V3lectronics/SPIRIT/branding/headphonejack.png

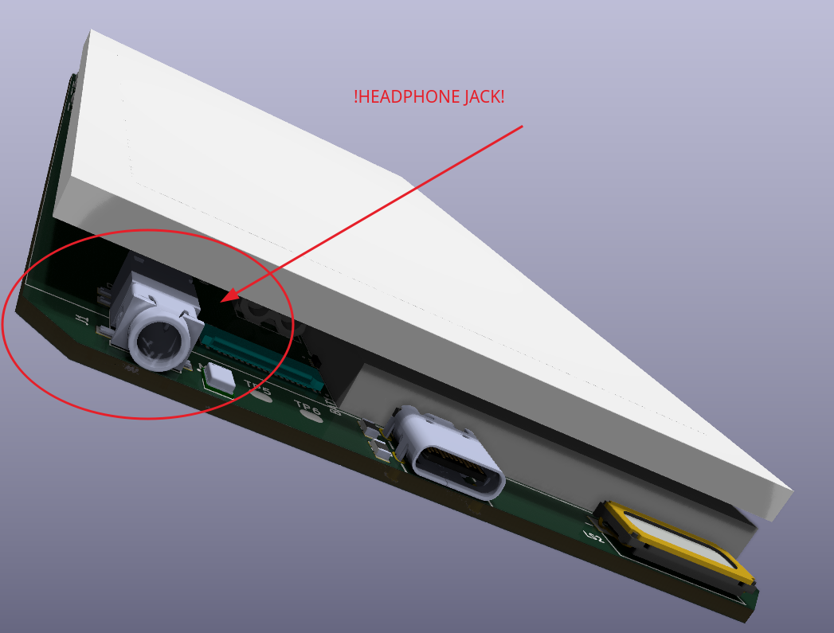
branding/headphonejack.png
