V3lectronics/SPIRIT/EDA-kicad/component-libs/SPIRIT-3D-models/CC0805MKX5R5BB476-capacitor.STEP

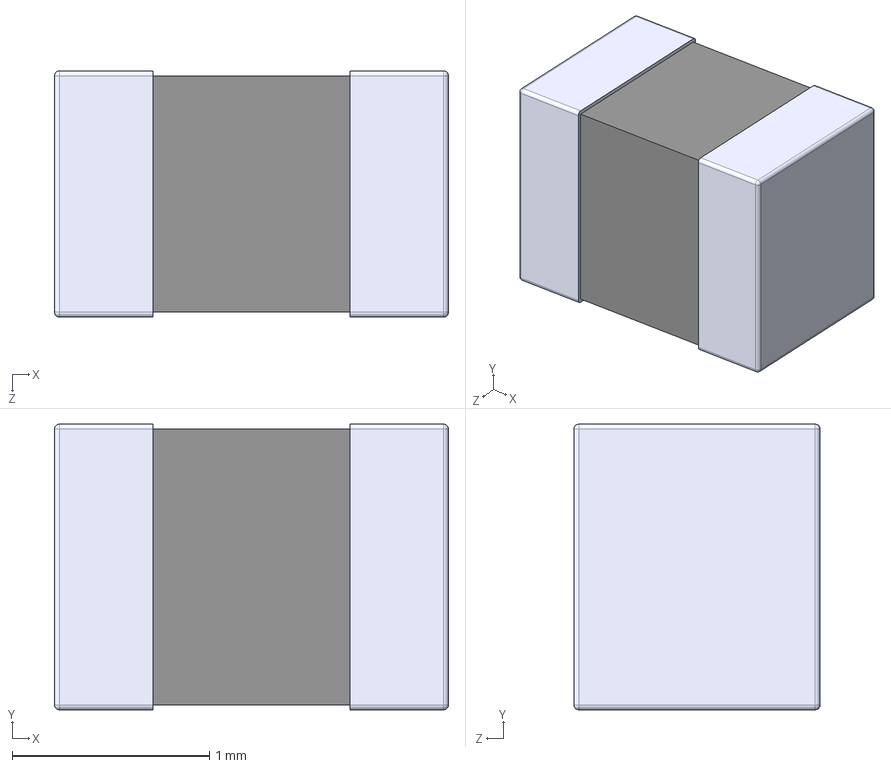
[picture p25: CAD file, 2025-09-16]
EDA-kicad/component-libs/SPIRIT-3D-models/CC0805MKX5R5BB476-capacitor.STEP
2.00 x 1.45 x 1.25 mm
