V3lectronics/SPIRIT/EDA-kicad/component-libs/SPIRIT-3D-models/MP3429GL.step

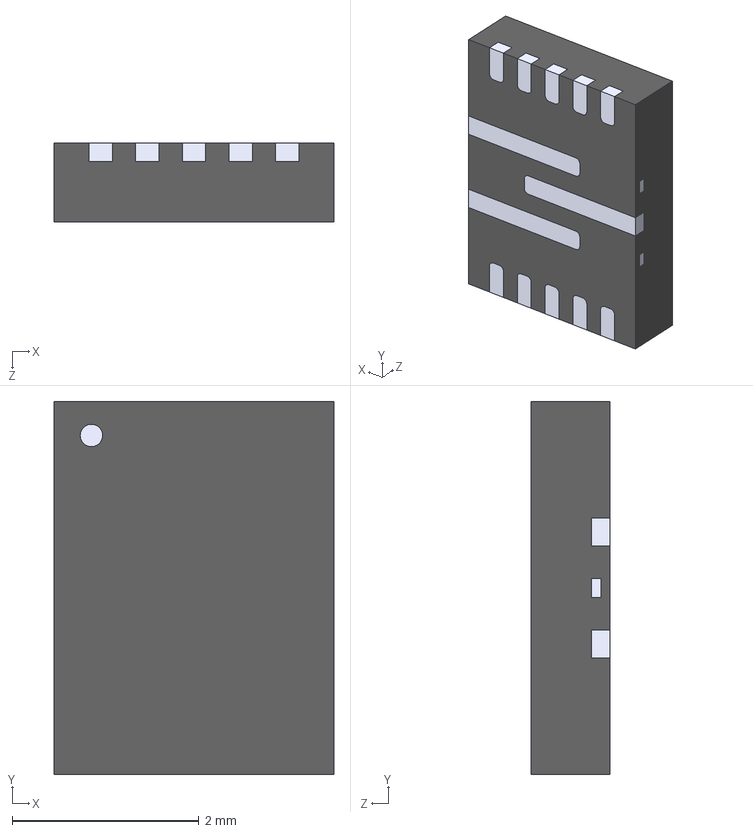
[picture p26: CAD file, 2025-09-12]
EDA-kicad/component-libs/SPIRIT-3D-models/MP3429GL.step
3.00 x 4.00 x 0.85 mm
