V3lectronics/SPIRIT/EDA-kicad/component-libs/SPIRIT-3D-models/BSC0902NSIATMA1-PG-TDSON-8-6.step

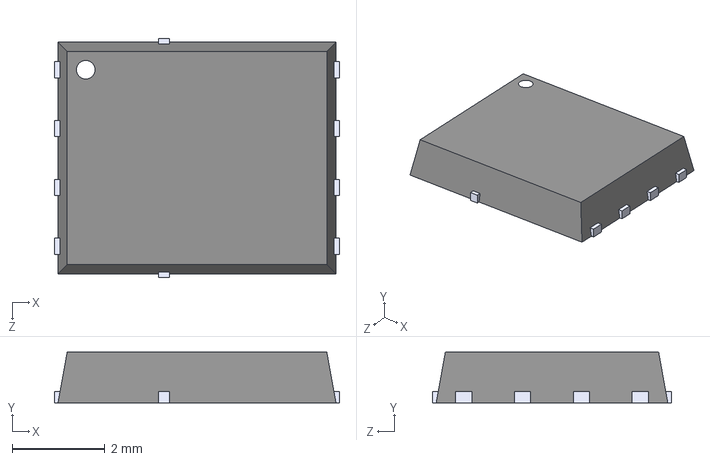
[picture p27: CAD file, 2025-09-05]
EDA-kicad/component-libs/SPIRIT-3D-models/BSC0902NSIATMA1-PG-TDSON-8-6.step
6.15 x 1.10 x 5.15 mm
