V3lectronics/SPIRIT/EDA-kicad/component-libs/SPIRIT-3D-models/0603-resistor.step

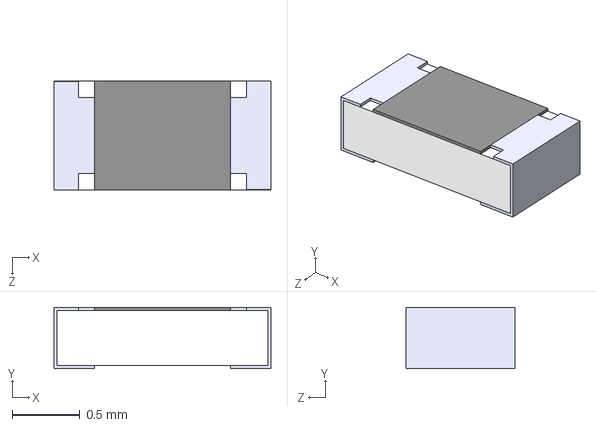
[picture p28: CAD file, 2025-09-04]
EDA-kicad/component-libs/SPIRIT-3D-models/0603-resistor.step
1.60 x 0.45 x 0.8 mm
