V3lectronics/SPIRIT/EDA-kicad/component-libs/SPIRIT-3D-models/100K-0805-resistor-ERA6AEB104V.step

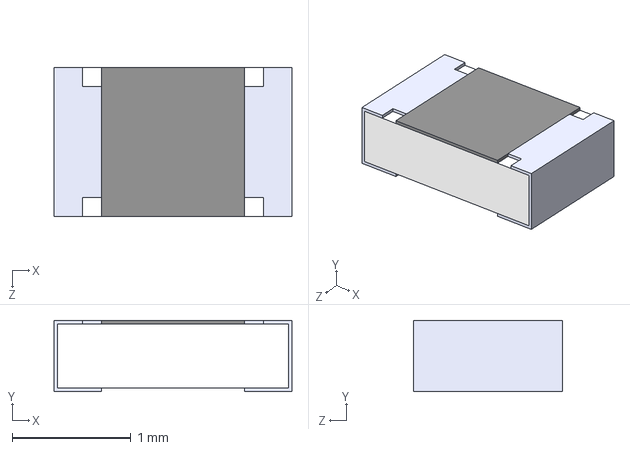
[picture p29: CAD file, 2025-09-02]
EDA-kicad/component-libs/SPIRIT-3D-models/100K-0805-resistor-ERA6AEB104V.step
2.00 x 0.6 x 1.25 mm
