V3lectronics/SPIRIT/EDA-kicad/component-libs/SPIRIT-3D-models/0603-capacitor.step

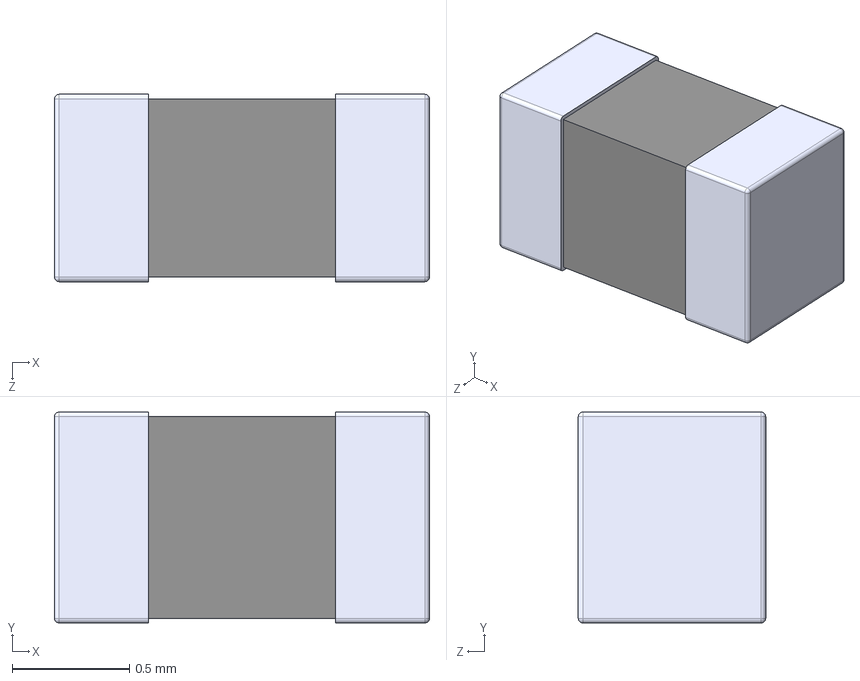
[picture p30: CAD file, 2025-09-02]
EDA-kicad/component-libs/SPIRIT-3D-models/0603-capacitor.step
1.60 x 0.9 x 0.8 mm
