V3lectronics/SPIRIT/EDA-kicad/component-libs/SPIRIT-3D-models/USB-4-0-CX90MW9-24P1.step

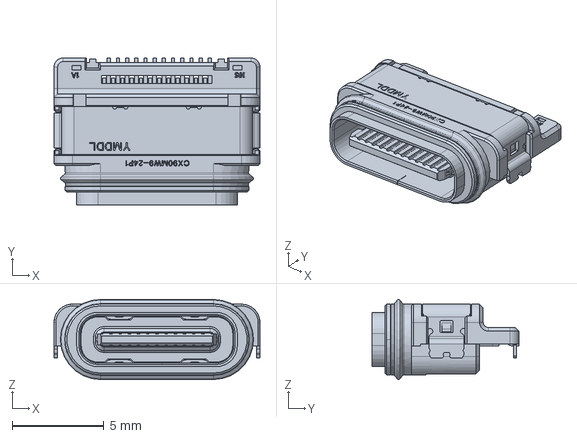
[picture p31: CAD file, 2025-08-21]
EDA-kicad/component-libs/SPIRIT-3D-models/USB-4-0-CX90MW9-24P1.step
11.2 x 8.00 x 4.35 mm
