V3lectronics/SPIRIT/EDA-kicad/component-libs/SPIRIT-3D-models/EG25GGC-128-SGNS.step

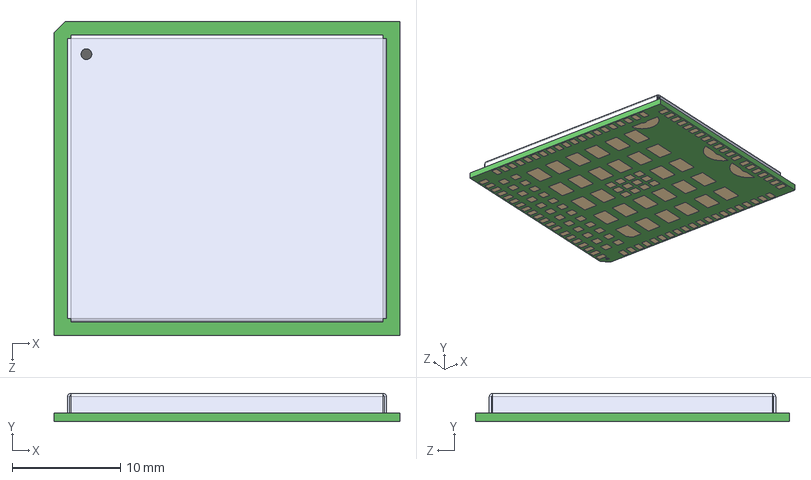
[picture p32: CAD file, 2025-08-20]
EDA-kicad/component-libs/SPIRIT-3D-models/EG25GGC-128-SGNS.step
32.0 x 2.60 x 29.0 mm
