V3lectronics/SPIRIT/EDA-kicad/component-libs/SPIRIT-3D-models/display-RK055AHD091-CTG-ribbon-tucked.step

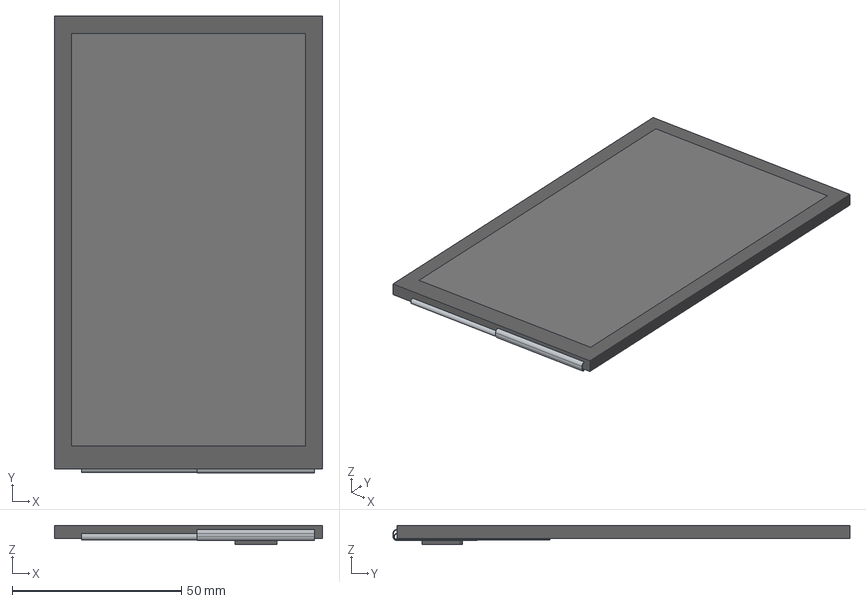
[picture p33: CAD file, 2025-08-14]
EDA-kicad/component-libs/SPIRIT-3D-models/display-RK055AHD091-CTG-ribbon-tucked.step
79.2 x 135.1 x 5.70 mm
ribbon-cable-back
ribbon-cable-lcd
component area
connector
screen-glass
screen-body
