V3lectronics/SPIRIT/EDA-kicad/component-libs/SPIRIT-3D-models/display-RK055AHD091-CTG-ribbon-straight.step

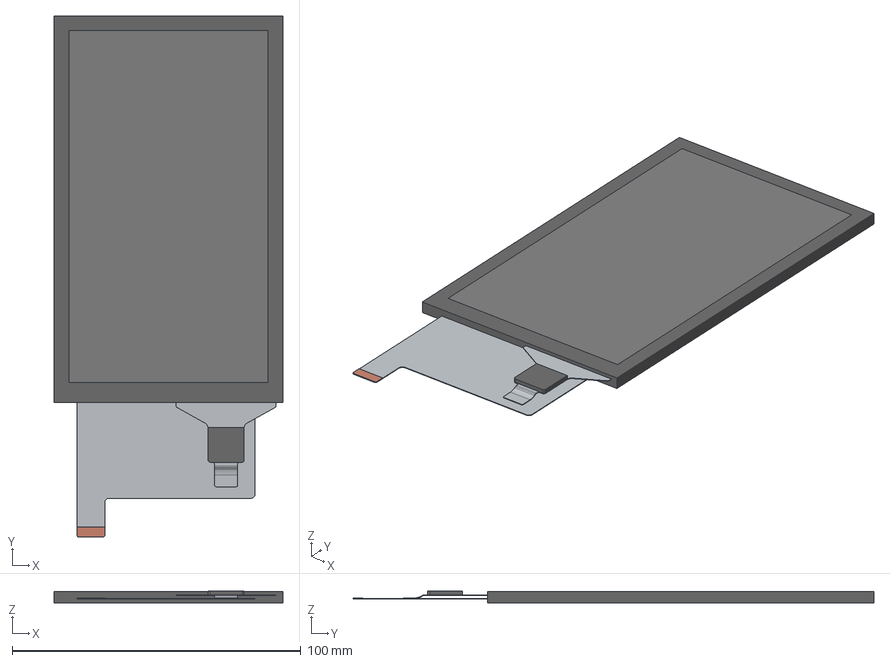
[picture p34: CAD file, 2025-08-14]
EDA-kicad/component-libs/SPIRIT-3D-models/display-RK055AHD091-CTG-ribbon-straight.step
79.2 x 180.5 x 4.00 mm
ribbon-cable-back001
ribbon-cable-lcd001
component area001
connector001
screen-glass001
screen-body001
