V3lectronics/SPIRIT/EDA-kicad/component-libs/SPIRIT-3D-models/molex-10pin-fingerprint-scanner-connector-5034801000.stp

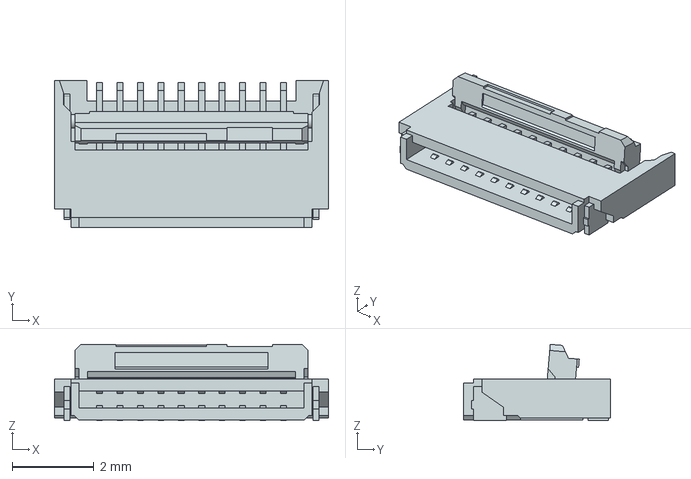
[picture p35: CAD file, 2025-08-13]
EDA-kicad/component-libs/SPIRIT-3D-models/molex-10pin-fingerprint-scanner-connector-5034801000.stp
6.70 x 3.60 x 1.87 mm
