V3lectronics/SPIRIT/EDA-kicad/component-libs/SPIRIT-3D-models/finger print scanner module.stp

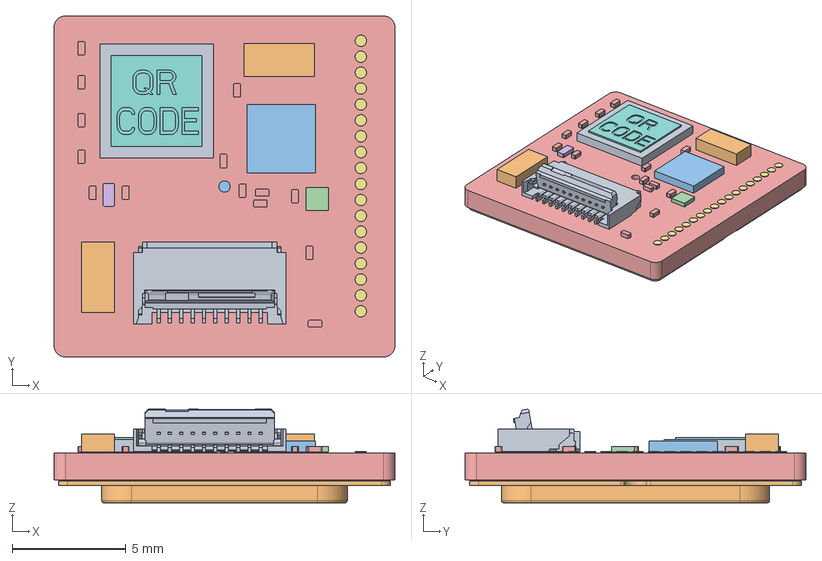
[picture p36: CAD file, 2025-08-13]
EDA-kicad/component-libs/SPIRIT-3D-models/finger print scanner module.stp
15.0 x 15.0 x 4.13 mm
2D_1_1_1_1_1_1_1_1_1_1_1_1_1_1_
PRT0003_1_1_1_1_1_1_1_1_1_1_1_1
PRT0003_1_2_1_1_1_1_1_1_1_1_1_1
PRT0003_1_3_1_1_1_1_1_1_1_1_1_1
PRT0003_1_7_1_1_1_1_1_1_1_1_1_1
PRT0003_1_11_1_1_1_1_1_1_1_1_1_
PRT0003_1_13_1_1_1_1_1_1_1_1_1_
PRT0003_1_14_1_1_1_1_1_1_1_1_1_
PRT0003_1_15_1_1_1_1_1_1_1_1_1_
PRT0003_1_16_1_1_1_1_1_1_1_1_1_
PRT0003_1_17_1_1_1_1_1_1_1_1_1_
PRT0003_1_18_1_1_1_1_1_1_1_1_1_
PRT0003_1_19_1_1_1_1_1_1_1_1_1_
PRT0003_1_20_1_1_1_1_1_1_1_1_1_
TP_POINT_1_ASM_1_ASM_1_1_1_1_1_
QR_1_1_1_1_1_1_1_1_1_1_1_1_1
BEZEL_1_1_1_1_1_1_1_1_1_1_1_1_1
LGA_1_1_1_1_1_1_1_1_1_1_1_1_1_1
COATING_1_1_1_1_1_1_1_1_1_1_1_1
PRT0001_1_1
