V3lectronics/SPIRIT/EDA-kicad/component-libs/SPIRIT-3D-models/Flash-LED-Lumiled.stp

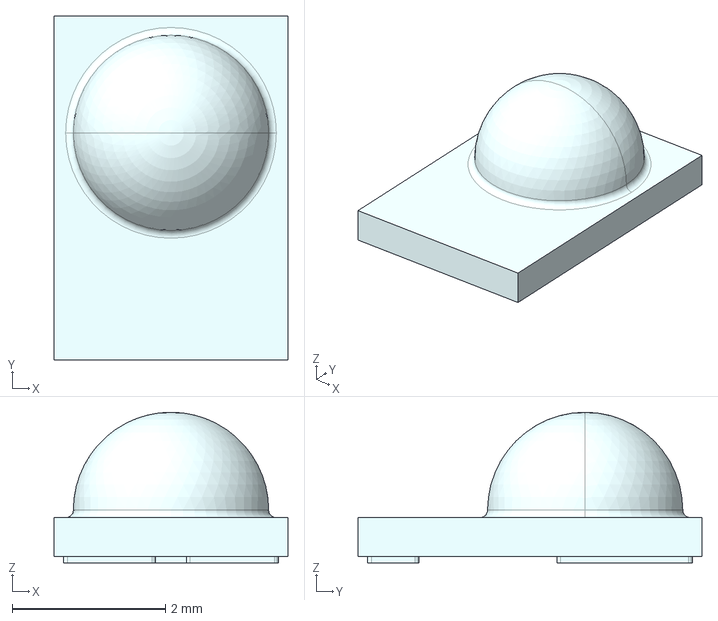
[picture p37: CAD file, 2025-08-13]
EDA-kicad/component-libs/SPIRIT-3D-models/Flash-LED-Lumiled.stp
3.05 x 4.49 x 1.96 mm
