V3lectronics/SPIRIT/EDA-kicad/component-libs/SPIRIT-3D-models/Battery_lp685077jupcm2.step

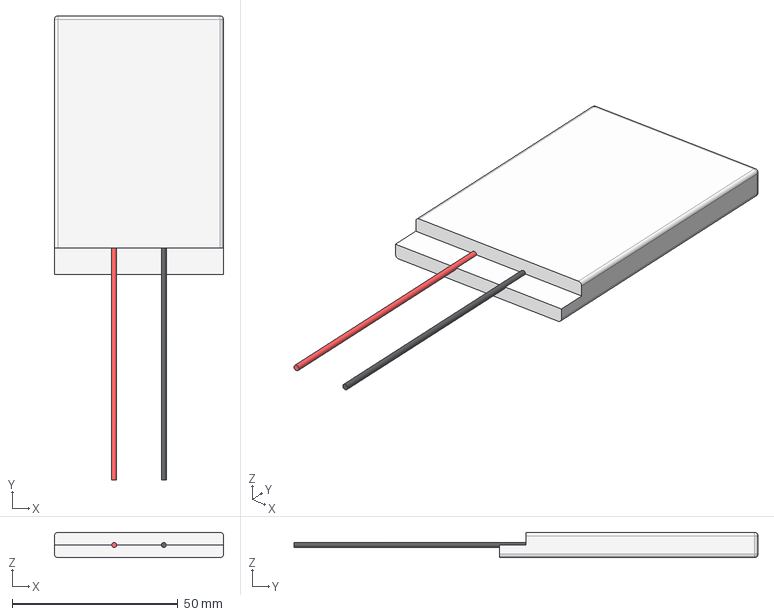
[picture p38: CAD file, 2025-08-13]
EDA-kicad/component-libs/SPIRIT-3D-models/Battery_lp685077jupcm2.step
51.0 x 140.0 x 7.56 mm
