V3lectronics/SPIRIT/EDA-kicad/component-libs/SPIRIT-3D-models/flyback-diode-1N4007W-T.step

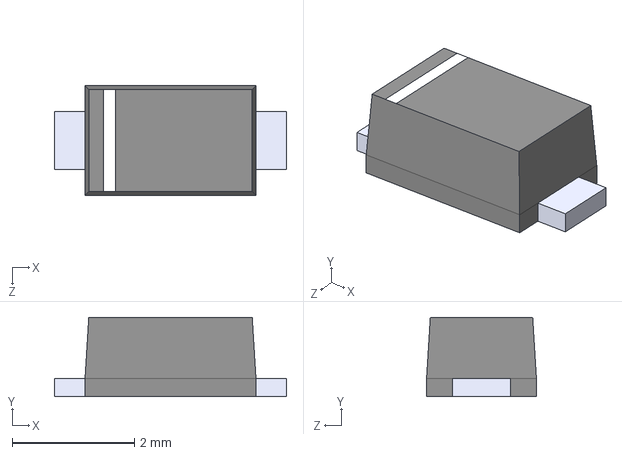
[picture p39: CAD file, 2025-07-15]
EDA-kicad/component-libs/SPIRIT-3D-models/flyback-diode-1N4007W-T.step
3.80 x 1.30 x 1.80 mm
