V3lectronics/SPIRIT/EDA-kicad/component-libs/SPIRIT-3D-models/gpio-driver-transistor-BSS816NWH6327XTSA1.STEP

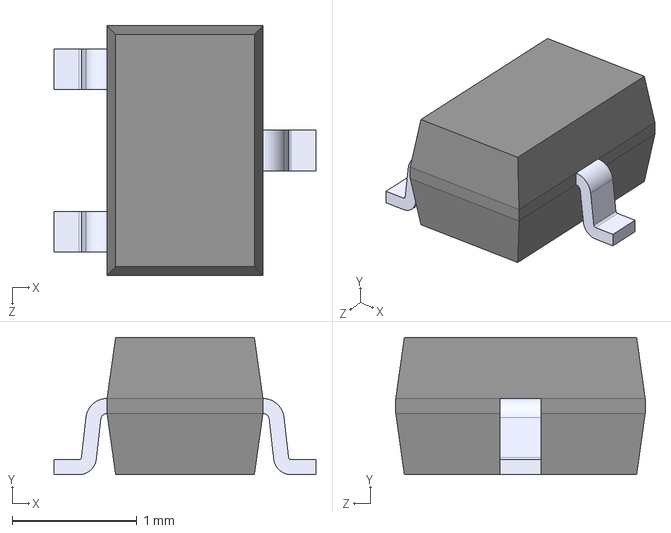
[picture p40: CAD file, 2025-07-15]
EDA-kicad/component-libs/SPIRIT-3D-models/gpio-driver-transistor-BSS816NWH6327XTSA1.STEP
2.10 x 1.10 x 2.00 mm
