V3lectronics/SPIRIT/EDA-kicad/component-libs/SPIRIT-3D-models/driver-transistor-SOT-723-MMBT2222AM3T5G-SOT-723_0P85X1P25_ONS.step

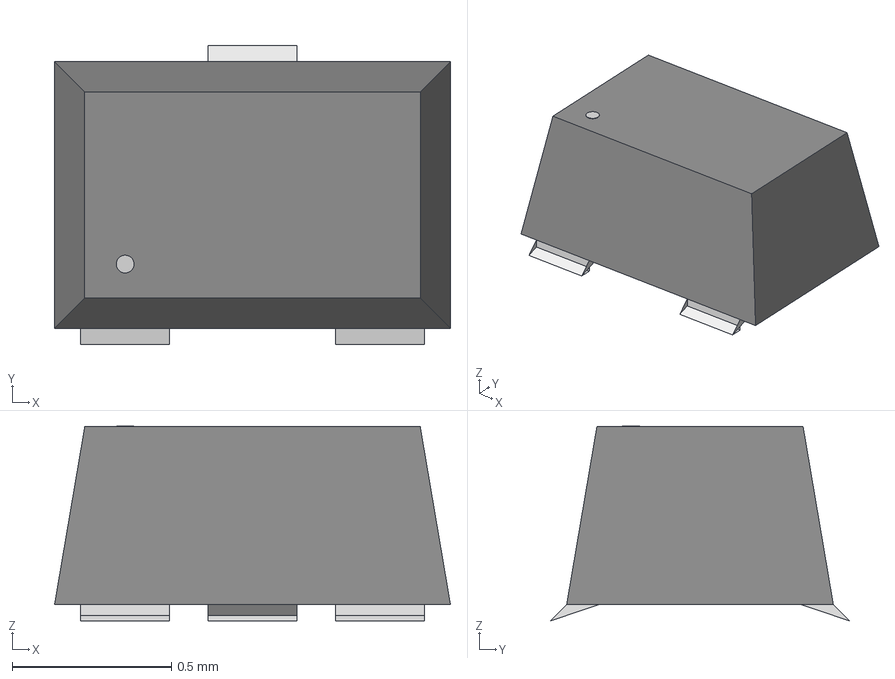
[picture p41: CAD file, 2025-07-15]
EDA-kicad/component-libs/SPIRIT-3D-models/driver-transistor-SOT-723-MMBT2222AM3T5G-SOT-723_0P85X1P25_ONS.step
1.24 x 0.94 x 0.612 mm
