V3lectronics/SPIRIT/EDA-kicad/component-libs/SPIRIT-3D-models/USBC-3-2-fix-USB4056-03-A_REVA2.step

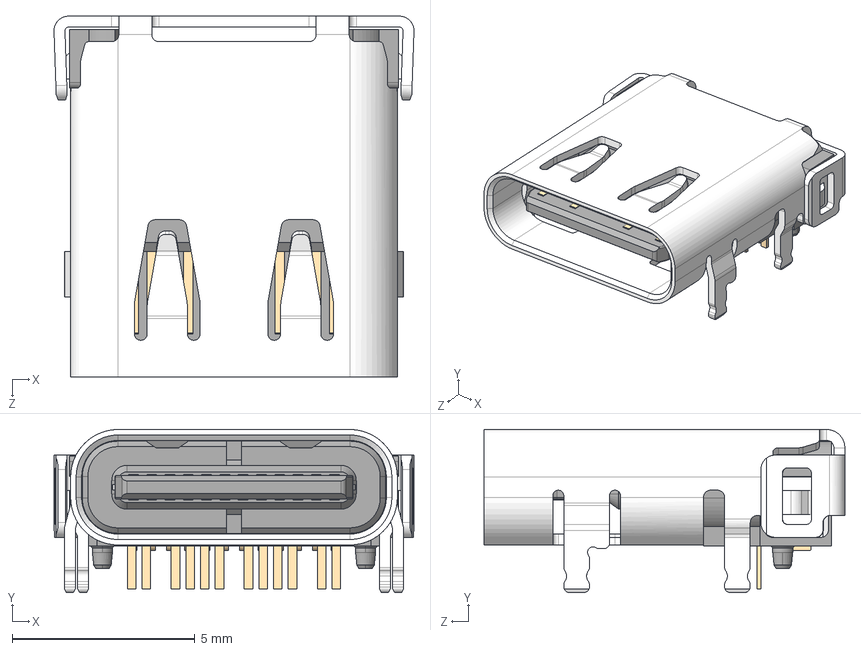
[picture p42: CAD file, 2025-07-01]
EDA-kicad/component-libs/SPIRIT-3D-models/USBC-3-2-fix-USB4056-03-A_REVA2.step
9.85 x 4.46 x 9.87 mm
