V3lectronics/SPIRIT/EDA-kicad/component-libs/SPIRIT-3D-models/pianoCHP-041TB.stp

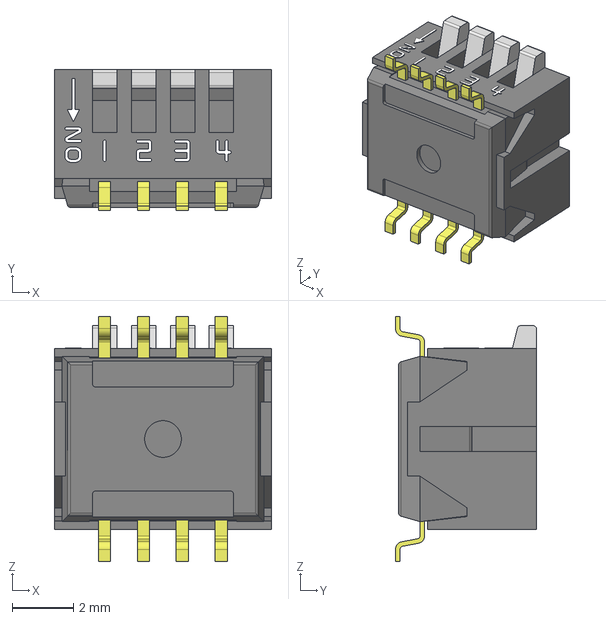
[picture p43: CAD file, 2025-07-01]
EDA-kicad/component-libs/SPIRIT-3D-models/pianoCHP-041TB.stp
7.10 x 4.60 x 8.00 mm
CHP-04-G-Lower-body
CHP-knobLower x 4
