V3lectronics/SPIRIT/EDA-kicad/component-libs/SPIRIT-3D-models/TVS-array-PUSB3FR6Z.step

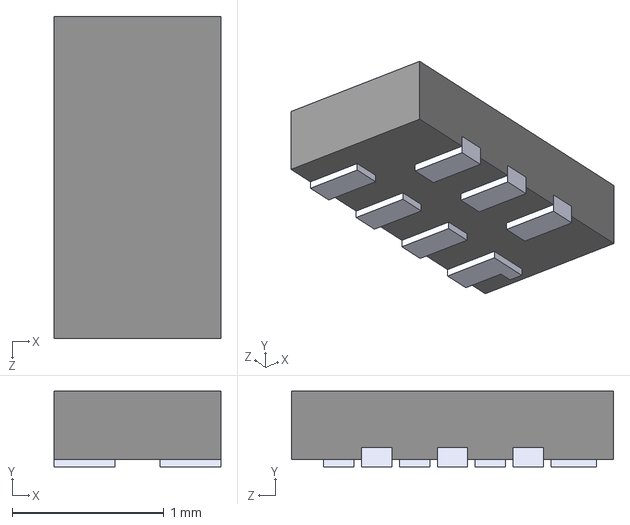
[picture p44: CAD file, 2025-01-05]
EDA-kicad/component-libs/SPIRIT-3D-models/TVS-array-PUSB3FR6Z.step
1.10 x 0.5 x 2.12 mm
