V3lectronics/SPIRIT/EDA-kicad/component-libs/SPIRIT-3D-models/usbC3-0.STEP

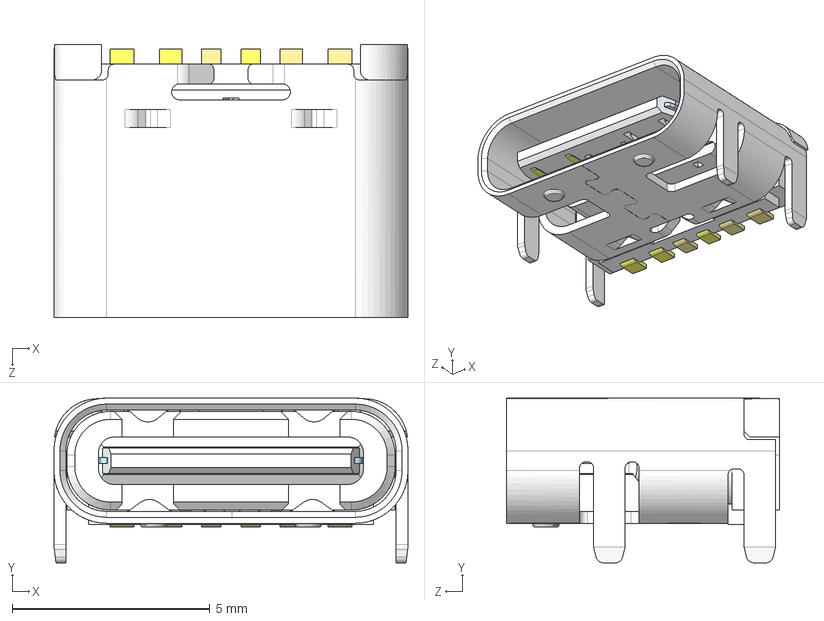
[picture p45: CAD file, 2025-01-05]
EDA-kicad/component-libs/SPIRIT-3D-models/usbC3-0.STEP
8.94 x 4.16 x 6.90 mm
