V3lectronics/SPIRIT/EDA-kicad/component-libs/SPIRIT-3D-models/USBC_capacitor_GRM033R60J334ME90D.step

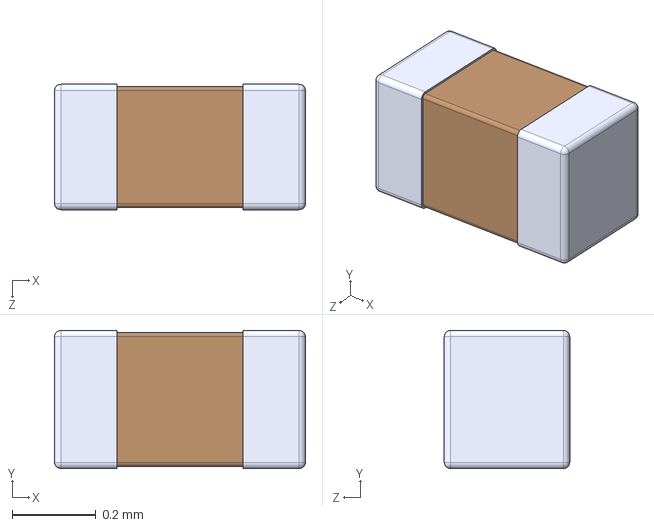
[picture p46: CAD file, 2025-01-05]
EDA-kicad/component-libs/SPIRIT-3D-models/USBC_capacitor_GRM033R60J334ME90D.step
0.6 x 0.33 x 0.3 mm
