V3lectronics/SPIRIT/EDA-kicad/component-libs/SPIRIT-3D-models/USB-ESD-protection-diode-PESD5V0C1USFYL-SOD962-2_DSN0603-2_NEX.step

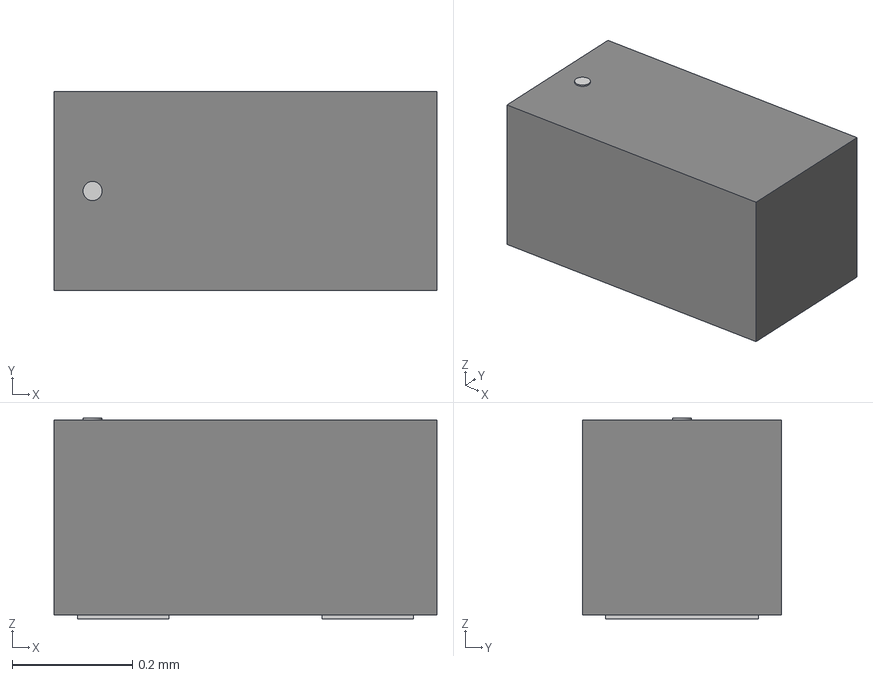
[picture p47: CAD file, 2025-01-05]
EDA-kicad/component-libs/SPIRIT-3D-models/USB-ESD-protection-diode-PESD5V0C1USFYL-SOD962-2_DSN0603-2_NEX.step
0.636 x 0.33 x 0.333 mm
