V3lectronics/SPIRIT/EDA-kicad/component-libs/SPIRIT-3D-models/TVSdiode-array-DQA0010A.stp

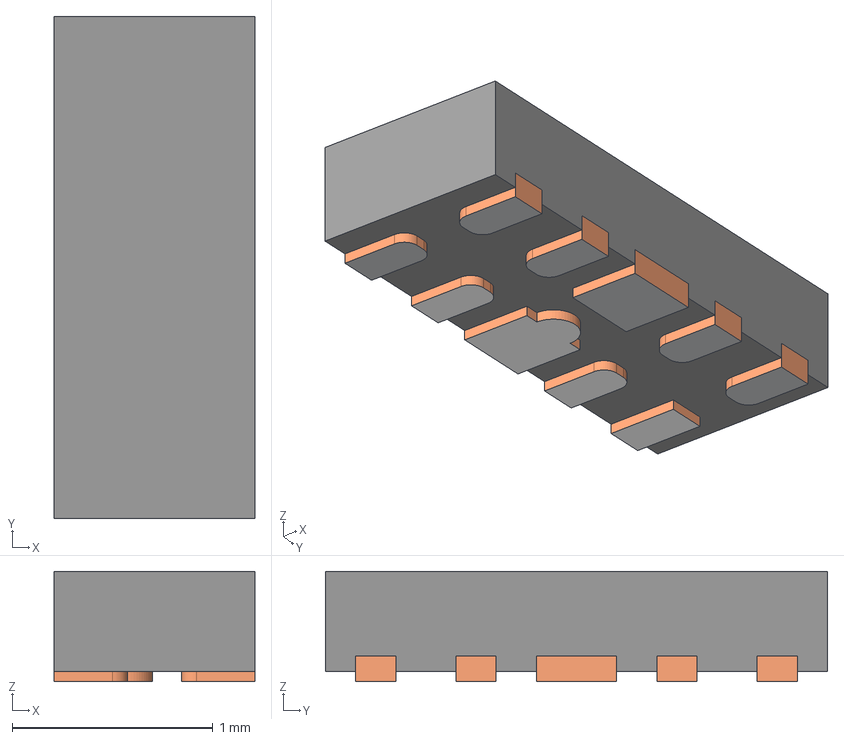
[picture p48: CAD file, 2024-12-01]
EDA-kicad/component-libs/SPIRIT-3D-models/TVSdiode-array-DQA0010A.stp
1.00 x 2.50 x 0.55 mm
BODY-SON
FRAME-DQA0010A
PIN1-ID
