V3lectronics/SPIRIT/EDA-kicad/component-libs/SPIRIT-3D-models/FPC15pin-1mm-pitch-F52Q-1A7H1-11015.STEP

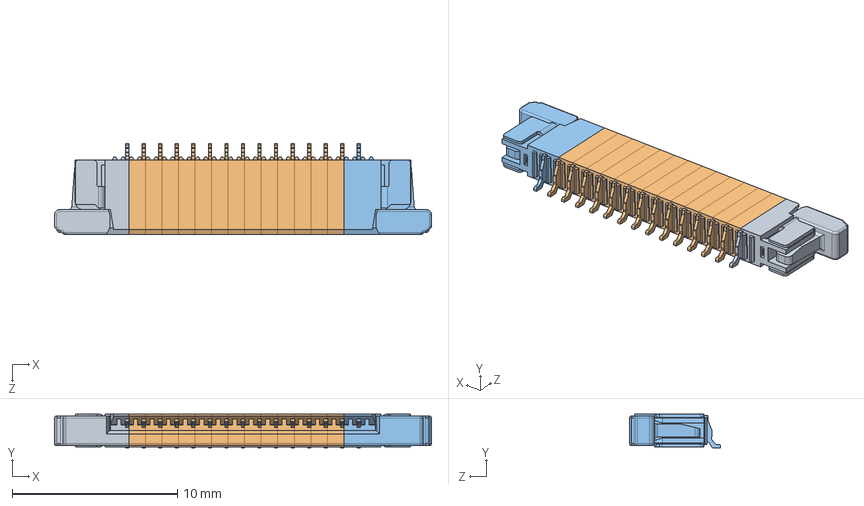
[picture p49: CAD file, 2024-12-01]
EDA-kicad/component-libs/SPIRIT-3D-models/FPC15pin-1mm-pitch-F52Q-1A7H1-11015.STEP
22.8 x 2.05 x 5.50 mm
F52Q_L.STEP
F52Q_M.STEP x 13
F52Q_R.STEP
