V3lectronics/SPIRIT/EDA-kicad/component-libs/SPIRIT-3D-models/Arducam16MPCamera.STEP

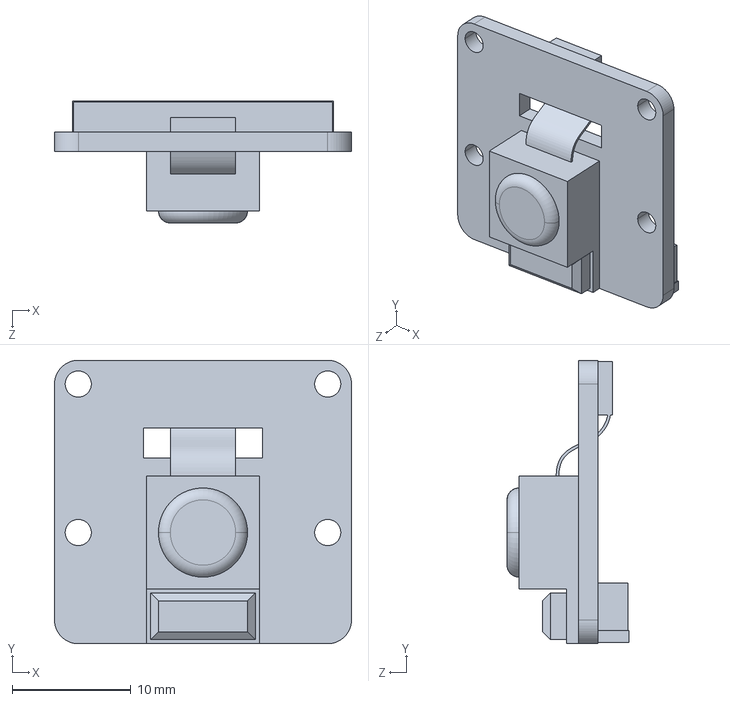
[picture p50: CAD file, 2024-12-01]
EDA-kicad/component-libs/SPIRIT-3D-models/Arducam16MPCamera.STEP
25.0 x 23.9 x 10.3 mm
