V3lectronics/SPIRIT/EDA-kicad/component-libs/SPIRIT-3D-models/35mmJACK-Same_Sky_SJ2-35894B-SMT-TR.step

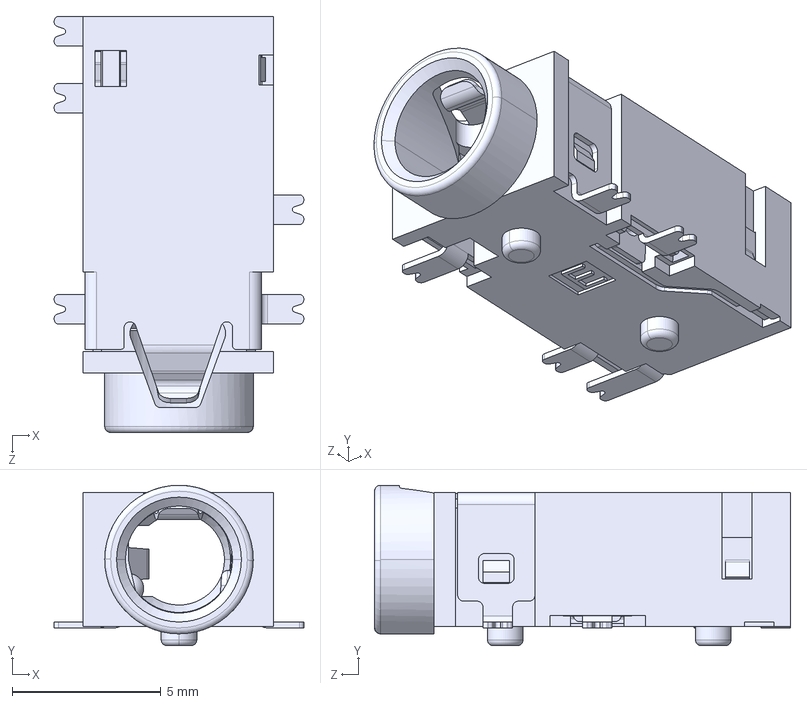
[picture p51: CAD file, 2024-11-07]
EDA-kicad/component-libs/SPIRIT-3D-models/35mmJACK-Same_Sky_SJ2-35894B-SMT-TR.step
8.40 x 5.40 x 14.0 mm
