V3lectronics/SPIRIT/EDA-kicad/component-libs/SPIRIT-3D-models/FPC15pins05pitch.step

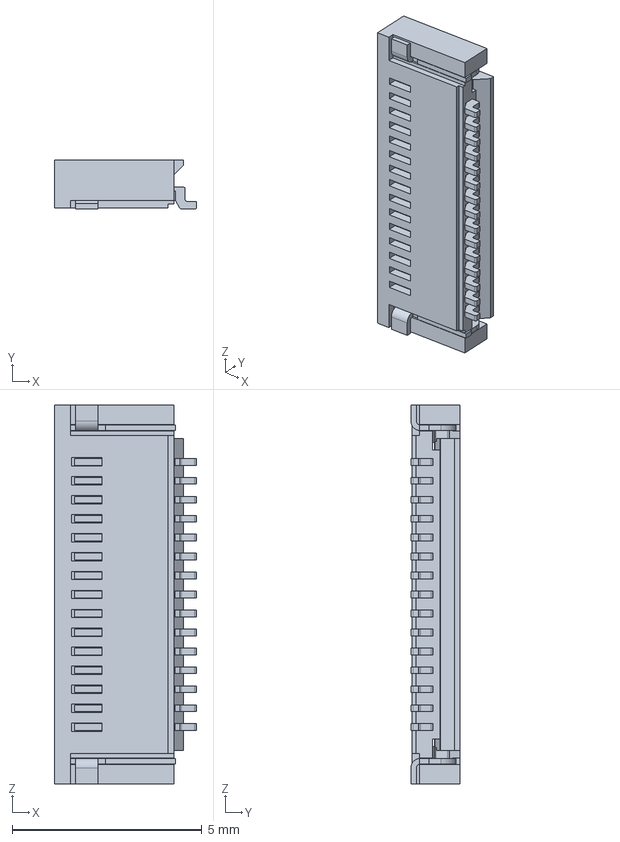
[picture p52: CAD file, 2024-11-07]
EDA-kicad/component-libs/SPIRIT-3D-models/FPC15pins05pitch.step
3.75 x 1.30 x 10.0 mm
