V3lectronics/SPIRIT/EDA-kicad/component-libs/SPIRIT-3D-models/INDICATOR-LED-QBLP601_MONO.step

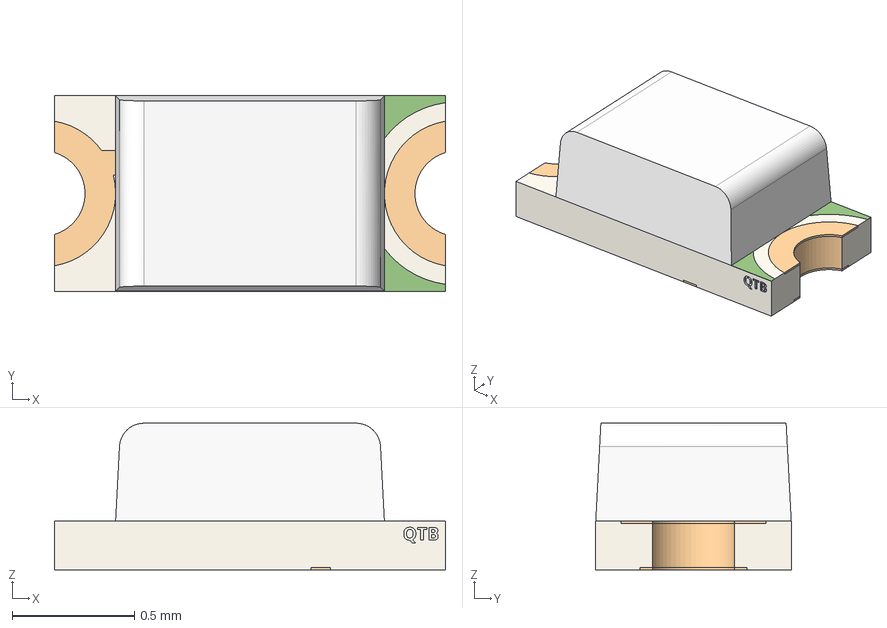
[picture p53: CAD file, 2024-10-05]
EDA-kicad/component-libs/SPIRIT-3D-models/INDICATOR-LED-QBLP601_MONO.step
1.60 x 0.8 x 0.6 mm
Substrate
Bottom Polarity
Top Polarity 2a x 2
Bottom Pad 2
Bottom Pad 1
Side Pad 2
Top Polarity 2b
Side Pad 1
Top Pad 1
Resin
