V3lectronics/SPIRIT/EDA-kicad/component-libs/SPIRIT-3D-models/KILL_SW_JS202011SCQN.step

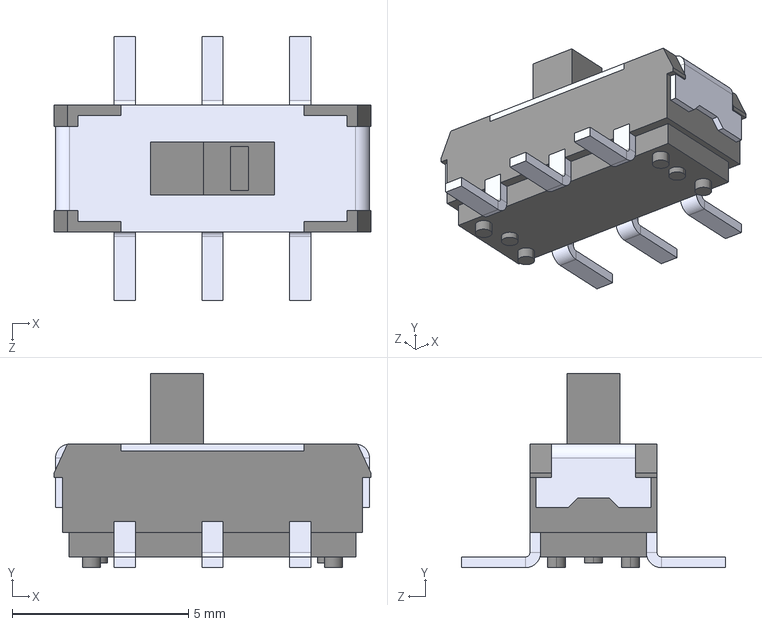
[picture p54: CAD file, 2024-10-05]
EDA-kicad/component-libs/SPIRIT-3D-models/KILL_SW_JS202011SCQN.step
8.99 x 5.51 x 7.49 mm
