V3lectronics/SPIRIT/EDA-kicad/component-libs/SPIRIT-3D-models/BAT-STEP-UP-UDFN8_2X2_MCH.step

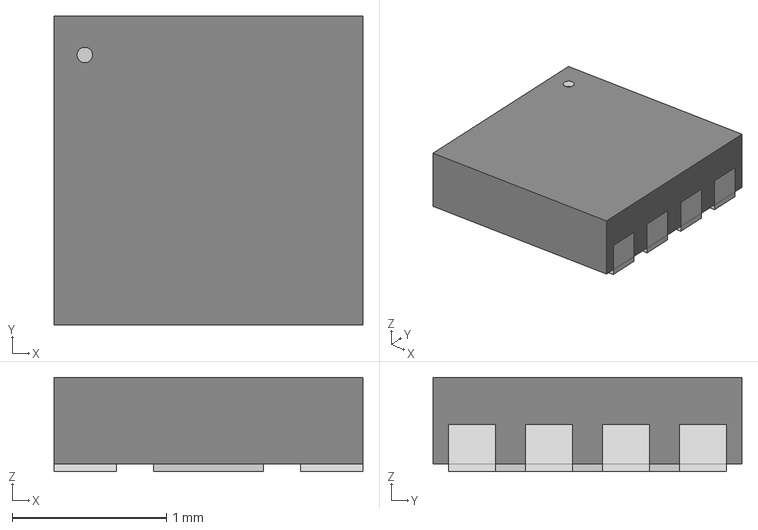
[picture p55: CAD file, 2024-10-05]
EDA-kicad/component-libs/SPIRIT-3D-models/BAT-STEP-UP-UDFN8_2X2_MCH.step
2.01 x 2.01 x 0.612 mm
