V3lectronics/SPIRIT/EDA-kicad/component-libs/SPIRIT-3D-models/CHARGER-SWITCHER-RTE0016C.stp

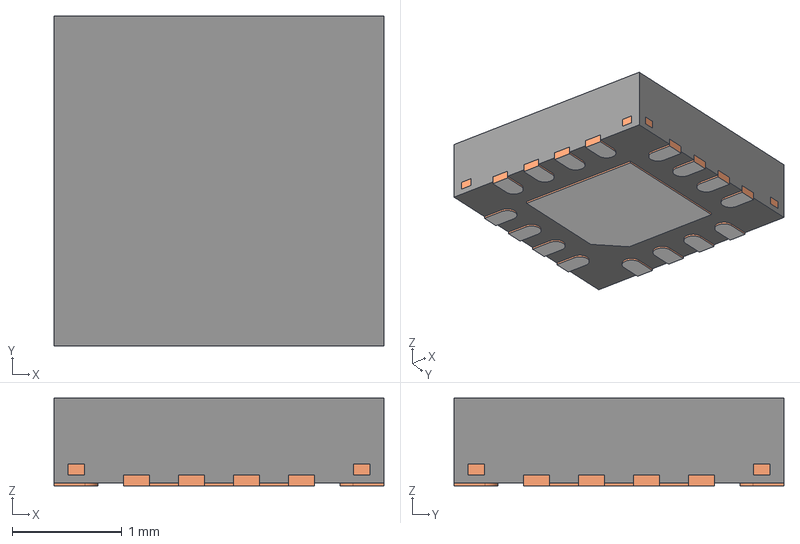
[picture p56: CAD file, 2024-10-05]
EDA-kicad/component-libs/SPIRIT-3D-models/CHARGER-SWITCHER-RTE0016C.stp
3.00 x 3.00 x 0.8 mm
BODY-QFN
FRAME-RTE0016C
PIN1-ID
