V3lectronics/SPIRIT/EDA-kicad/component-libs/SPIRIT-3D-models/DIPSWITCH-219-4M.STEP

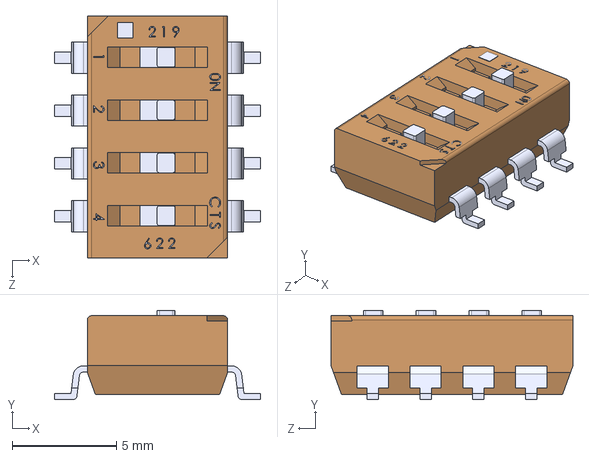
[picture p57: CAD file, 2024-10-05]
EDA-kicad/component-libs/SPIRIT-3D-models/DIPSWITCH-219-4M.STEP
9.91 x 4.28 x 11.6 mm
