V3lectronics/SPIRIT/EDA-kicad/component-libs/SPIRIT-3D-models/BAT-MONITOR-BQ27530YZFT-G1.STEP

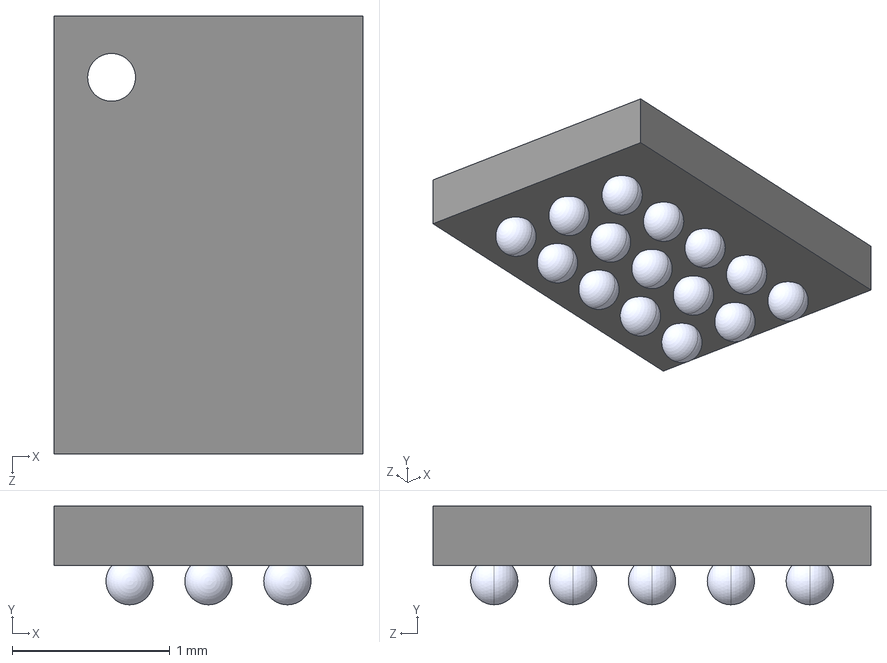
[picture p58: CAD file, 2024-09-21]
EDA-kicad/component-libs/SPIRIT-3D-models/BAT-MONITOR-BQ27530YZFT-G1.STEP
1.96 x 0.625 x 2.78 mm
