V3lectronics/SPIRIT/EDA-kicad/component-libs/SPIRIT-3D-models/VIBRATION-HD-EMB1205-3-SC-R.step

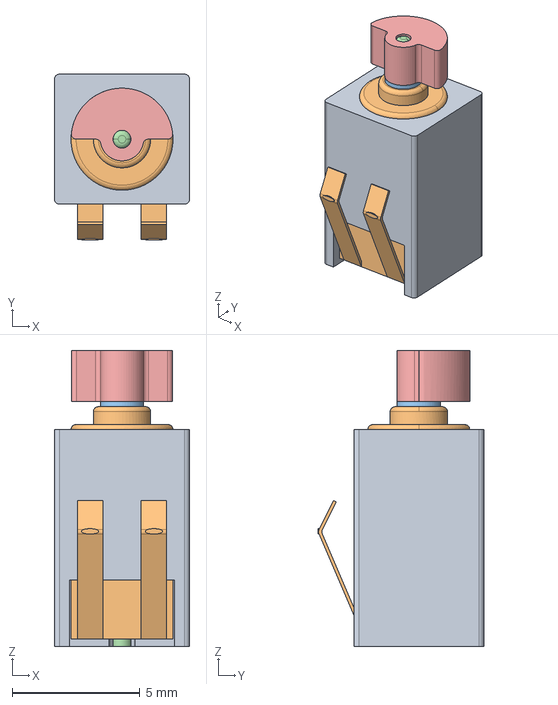
[picture p59: CAD file, 2024-09-21]
EDA-kicad/component-libs/SPIRIT-3D-models/VIBRATION-HD-EMB1205-3-SC-R.step
5.30 x 6.50 x 11.6 mm
