V3lectronics/SPIRIT/EDA-kicad/component-libs/SPIRIT-3D-models/STABILIZER-MC34063ADR.stp

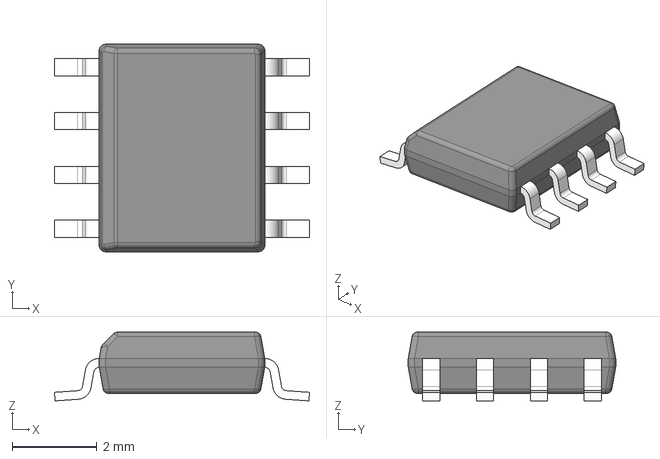
[picture p60: CAD file, 2024-09-21]
EDA-kicad/component-libs/SPIRIT-3D-models/STABILIZER-MC34063ADR.stp
6.02 x 4.90 x 1.63 mm
BODY-SO
LEAD-D0008A x 8
