V3lectronics/SPIRIT/EDA-kicad/component-libs/SPIRIT-3D-models/BAT-CONNECTOR-M-FLT-S22WR-00-REVT2.STEP

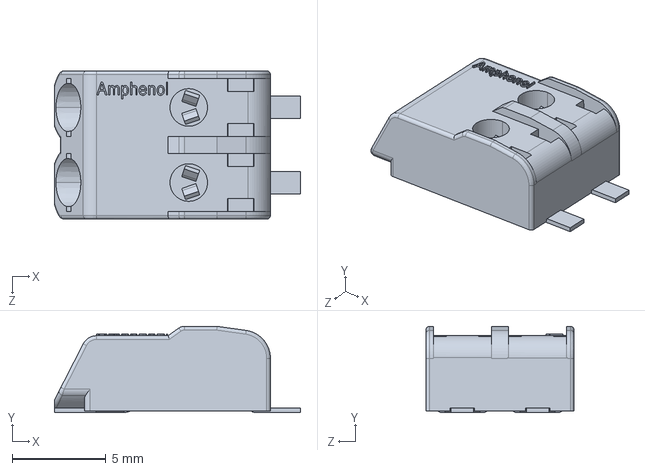
[picture p61: CAD file, 2024-09-21]
EDA-kicad/component-libs/SPIRIT-3D-models/BAT-CONNECTOR-M-FLT-S22WR-00-REVT2.STEP
13.1 x 4.60 x 7.90 mm
