V3lectronics/SPIRIT/EDA-kicad/component-libs/SPIRIT-3D-models/CHARGER-YFF49.step

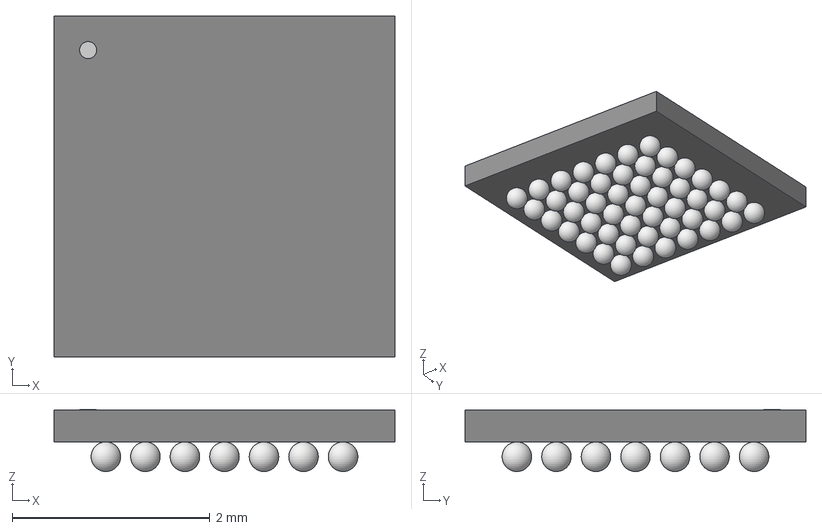
[picture p62: CAD file, 2024-09-21]
EDA-kicad/component-libs/SPIRIT-3D-models/CHARGER-YFF49.step
3.45 x 3.45 x 0.628 mm
