V3lectronics/SPIRIT/EDA-kicad/component-libs/SPIRIT-3D-models/buttonTL3330AFxxxQG.stp

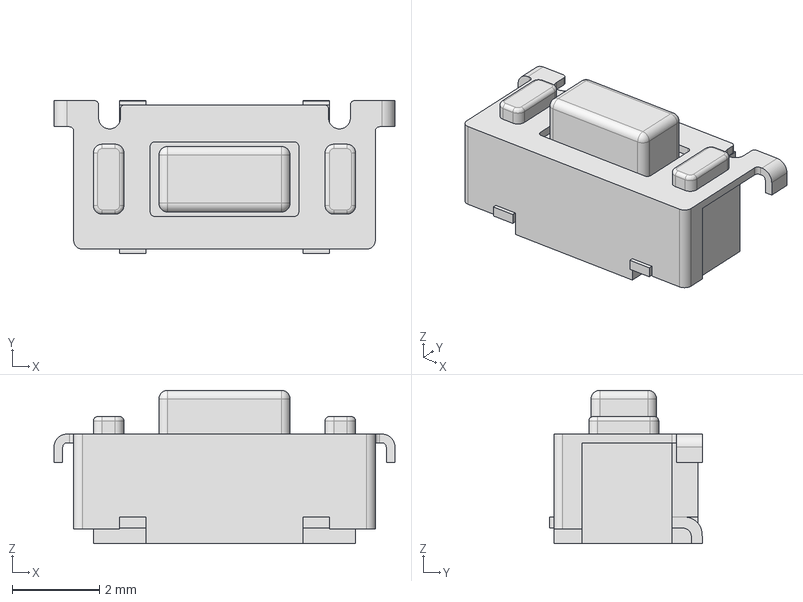
[picture p63: CAD file, 2024-09-13]
EDA-kicad/component-libs/SPIRIT-3D-models/buttonTL3330AFxxxQG.stp
7.80 x 3.50 x 3.51 mm
