V3lectronics/SPIRIT/EDA-kicad/component-libs/SPIRIT-3D-models/microphoneSPH0645LM4H-B.step

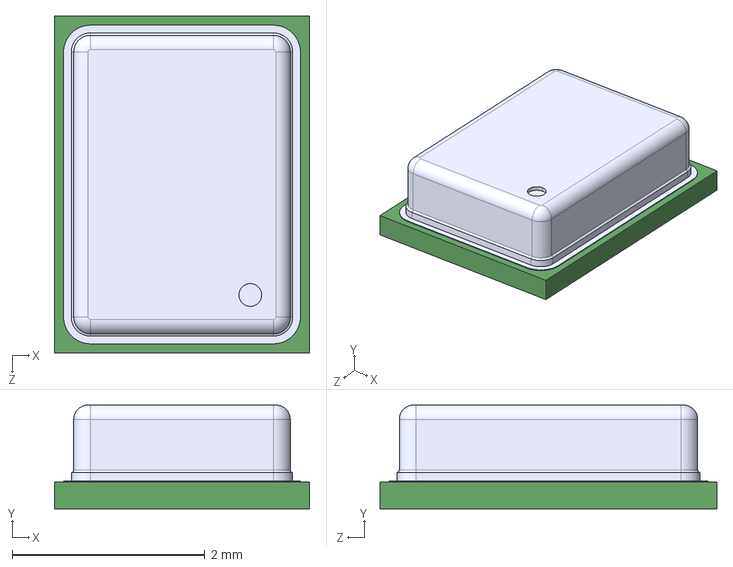
[picture p64: CAD file, 2024-09-13]
EDA-kicad/component-libs/SPIRIT-3D-models/microphoneSPH0645LM4H-B.step
2.65 x 1.08 x 3.50 mm
