V3lectronics/SPIRIT/EDA-kicad/component-libs/SPIRIT-3D-models/screenRK055AHD091.step

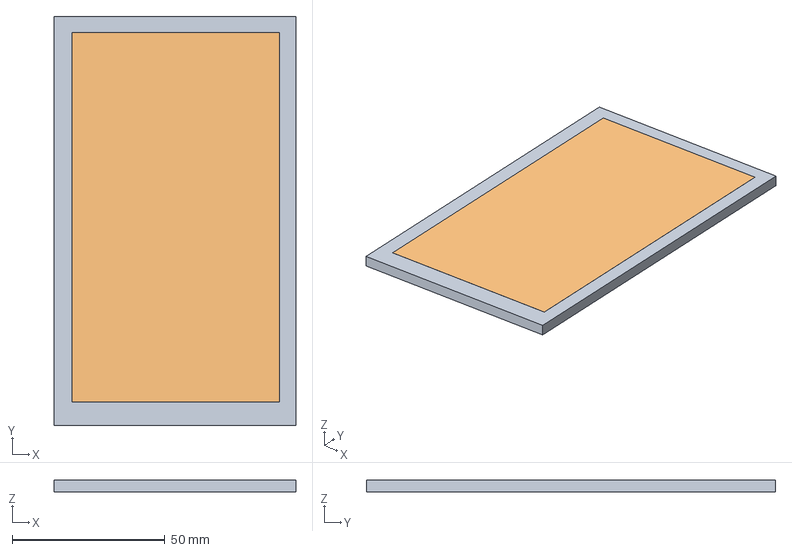
[picture p65: CAD file, 2024-09-13]
EDA-kicad/component-libs/SPIRIT-3D-models/screenRK055AHD091.step
79.2 x 134.0 x 3.90 mm
