V3lectronics/SPIRIT/EDA-kicad/component-libs/SPIRIT-3D-models/10-FPC.stp

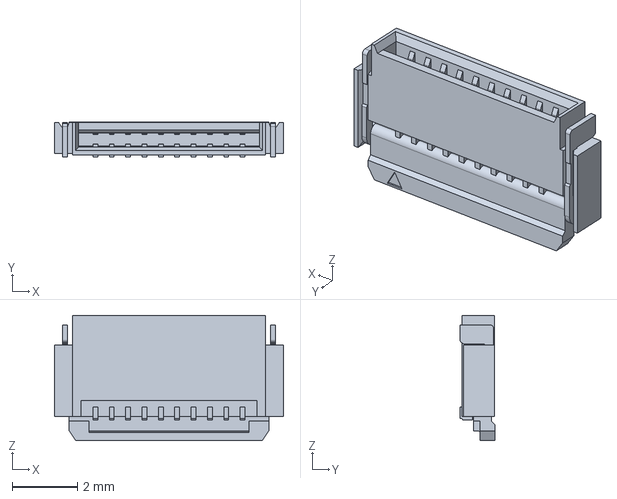
[picture p66: CAD file, 2024-09-13]
EDA-kicad/component-libs/SPIRIT-3D-models/10-FPC.stp
7.00 x 1.06 x 3.83 mm
