V3lectronics/SPIRIT/EDA-kicad/component-libs/SPIRIT-3D-models/FPC31-FH72-31S-0.3SHW.step

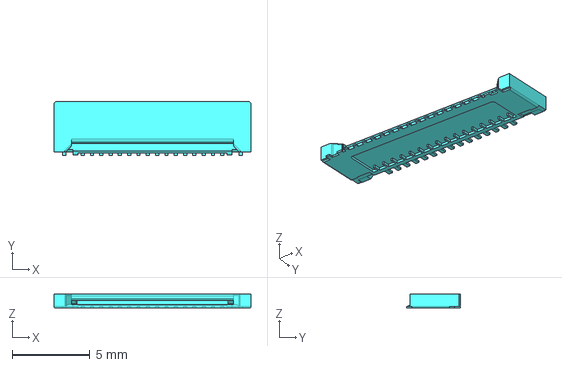
[picture p67: CAD file, 2024-09-13]
EDA-kicad/component-libs/SPIRIT-3D-models/FPC31-FH72-31S-0.3SHW.step
12.7 x 3.50 x 0.9 mm
