V3lectronics/SPIRIT/EDA-kicad/component-libs/SPIRIT-3D-models/bottom_FFT_FH12-22S-0.5SH(55).STEP

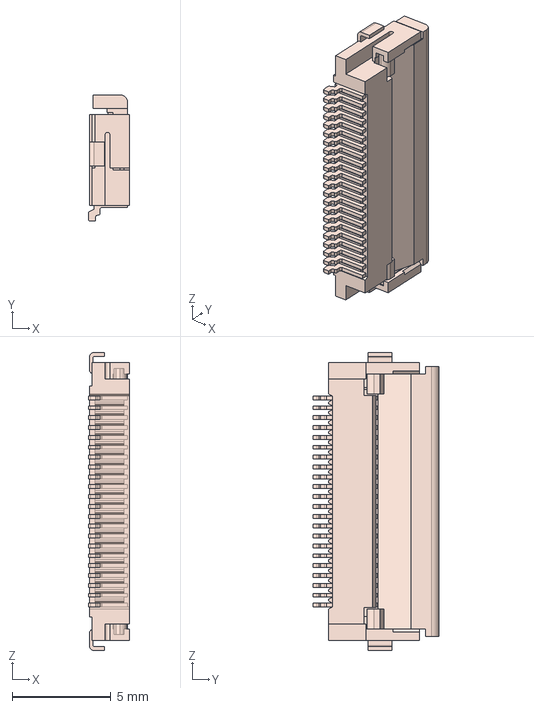
[picture p68: CAD file, 2024-09-09]
EDA-kicad/component-libs/SPIRIT-3D-models/bottom_FFT_FH12-22S-0.5SH(55).STEP
2.10 x 6.40 x 15.1 mm
