V3lectronics/SPIRIT/EDA-kicad/component-libs/SPIRIT-3D-models/PowerDI3333-8_Type-UX.STP

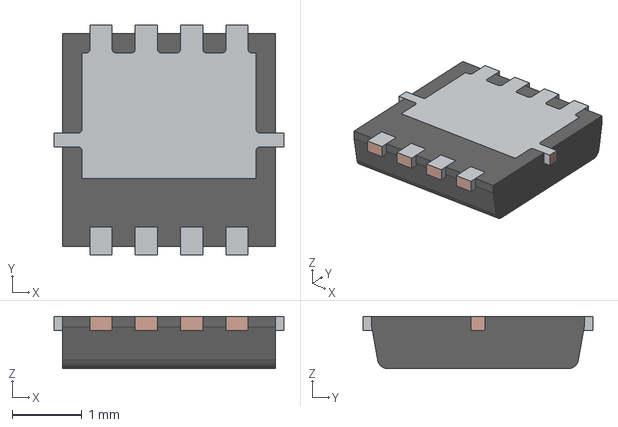
[picture p69: CAD file, 2024-09-09]
EDA-kicad/component-libs/SPIRIT-3D-models/PowerDI3333-8_Type-UX.STP
3.30 x 3.30 x 0.75 mm
Mold
LDF
