V3lectronics/SPIRIT/EDA-kicad/component-libs/SPIRIT-3D-models/UBAF-0110.STEP

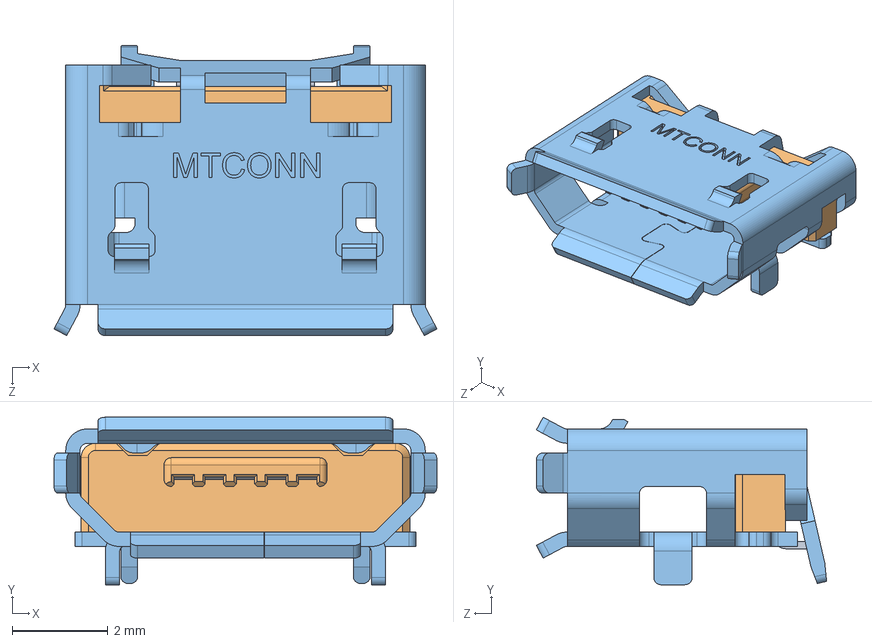
[picture p70: CAD file, 2024-09-09]
EDA-kicad/component-libs/SPIRIT-3D-models/UBAF-0110.STEP
7.99 x 3.49 x 6.06 mm
CONTACT___-1
CONTACT____1-1
CONTACT____2-1
CONTACT____3-1
CONTACT____4-1
HOUSING___-1
