V3lectronics/SPIRIT/EDA-kicad/component-libs/SPIRIT-3D-models/USB_C_USB4105-GF-A.step

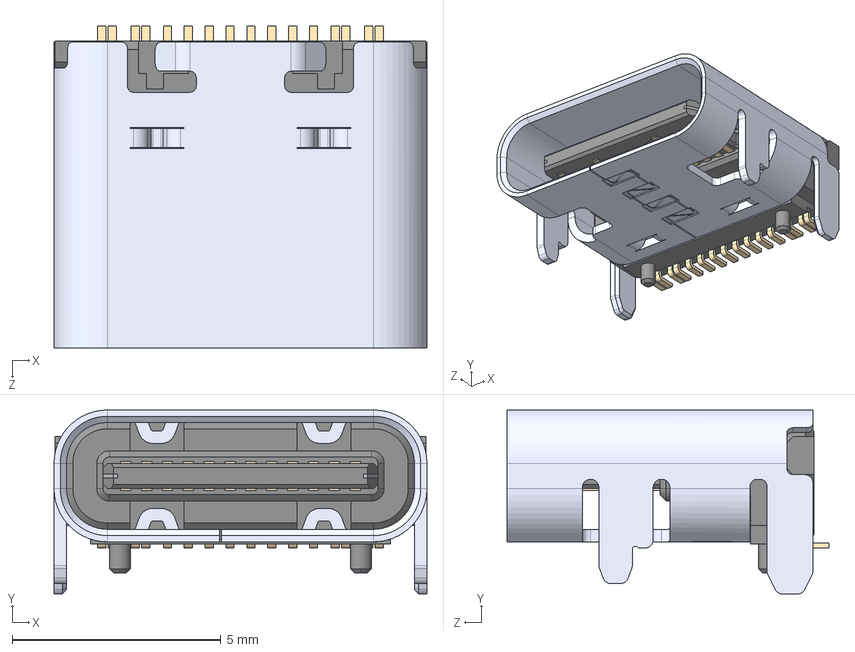
[picture p71: CAD file, 2024-09-09]
EDA-kicad/component-libs/SPIRIT-3D-models/USB_C_USB4105-GF-A.step
8.94 x 4.41 x 7.71 mm
