V3lectronics/SPIRIT/EDA-kicad/component-libs/SPIRIT-3D-models/TVS-SMBJ5.0A-TR.STEP

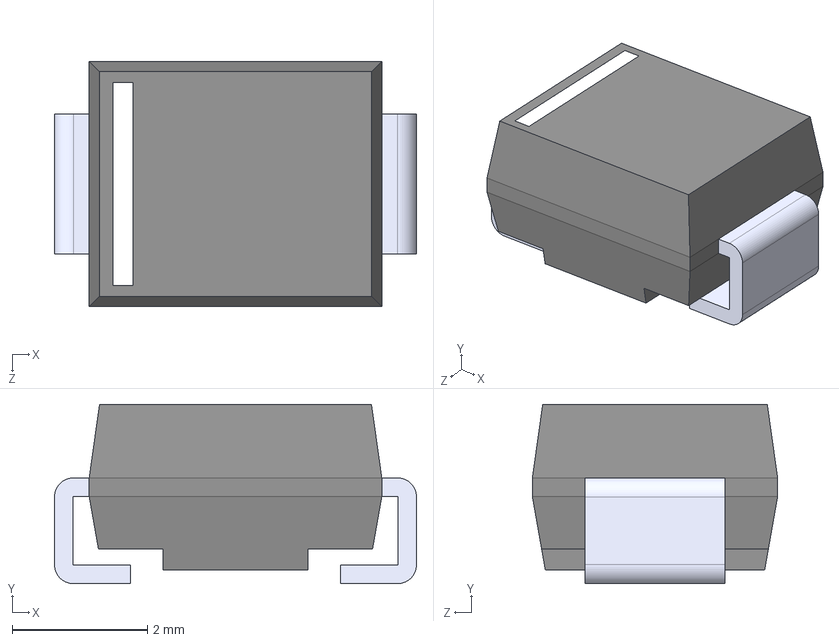
[picture p72: CAD file, 2024-09-09]
EDA-kicad/component-libs/SPIRIT-3D-models/TVS-SMBJ5.0A-TR.STEP
5.35 x 2.65 x 3.62 mm
