V3lectronics/SPIRIT/EDA-kicad/component-libs/SPIRIT-3D-models/speaker-CUI_DEVICES_CMR-15062S-67.step

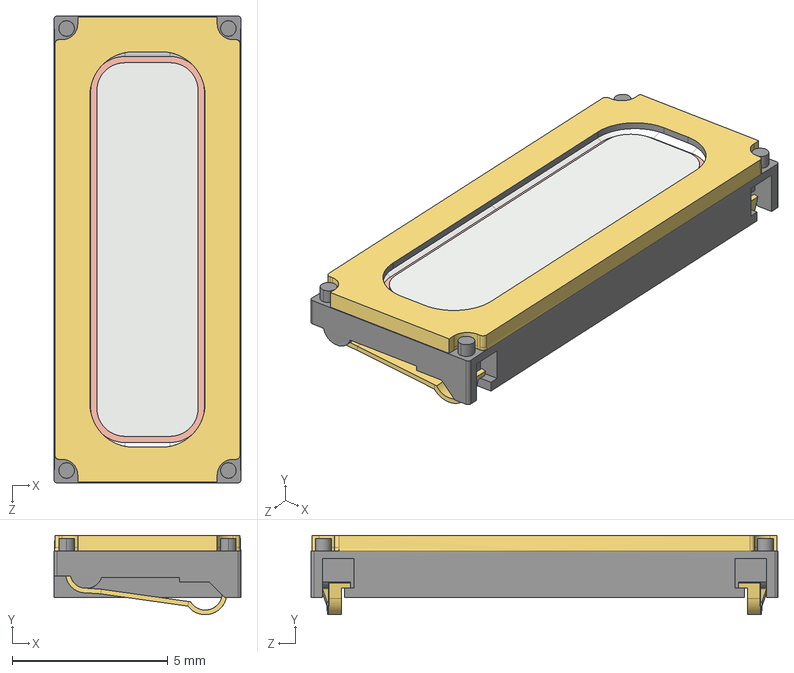
[picture p73: CAD file, 2024-09-09]
EDA-kicad/component-libs/SPIRIT-3D-models/speaker-CUI_DEVICES_CMR-15062S-67.step
6.00 x 2.55 x 15.0 mm
