V3lectronics/SPIRIT/EDA-kicad/component-libs/SPIRIT-3D-models/speaker-SP-1511S-1.step

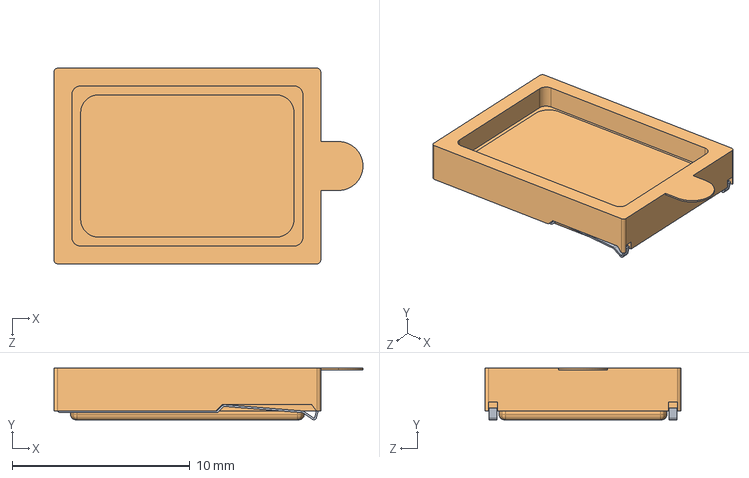
[picture p74: CAD file, 2024-09-09]
EDA-kicad/component-libs/SPIRIT-3D-models/speaker-SP-1511S-1.step
17.4 x 2.90 x 11.0 mm
