V3lectronics/SPIRIT/EDA-kicad/component-libs/SPIRIT-3D-models/DC-001-A-2.1mm-R.STEP

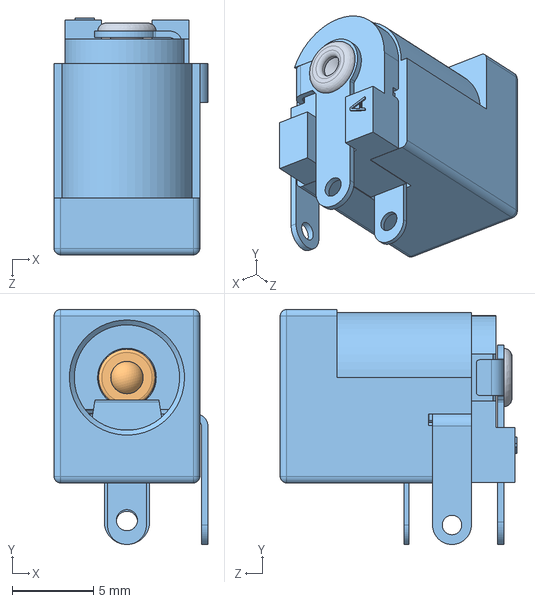
[picture p75: CAD file, 2024-09-09]
EDA-kicad/component-libs/SPIRIT-3D-models/DC-001-A-2.1mm-R.STEP
9.50 x 14.5 x 14.6 mm
