V3lectronics/SPIRIT/EDA-kicad/component-libs/SPIRIT-3D-models/battery-37V2AhLP504783JU-Body.step

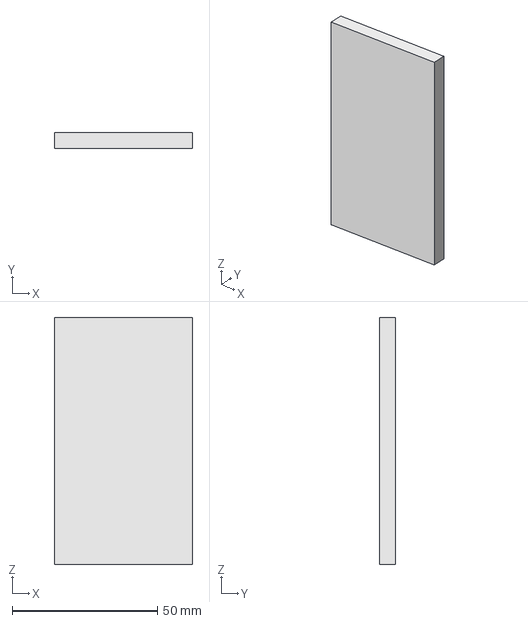
[picture p76: CAD file, 2024-09-09]
EDA-kicad/component-libs/SPIRIT-3D-models/battery-37V2AhLP504783JU-Body.step
47.5 x 5.60 x 85.0 mm
